RyzenGatto/Ai-HDL-MacroPad/Pictures/V1.5 MacroPad PCB.PNG

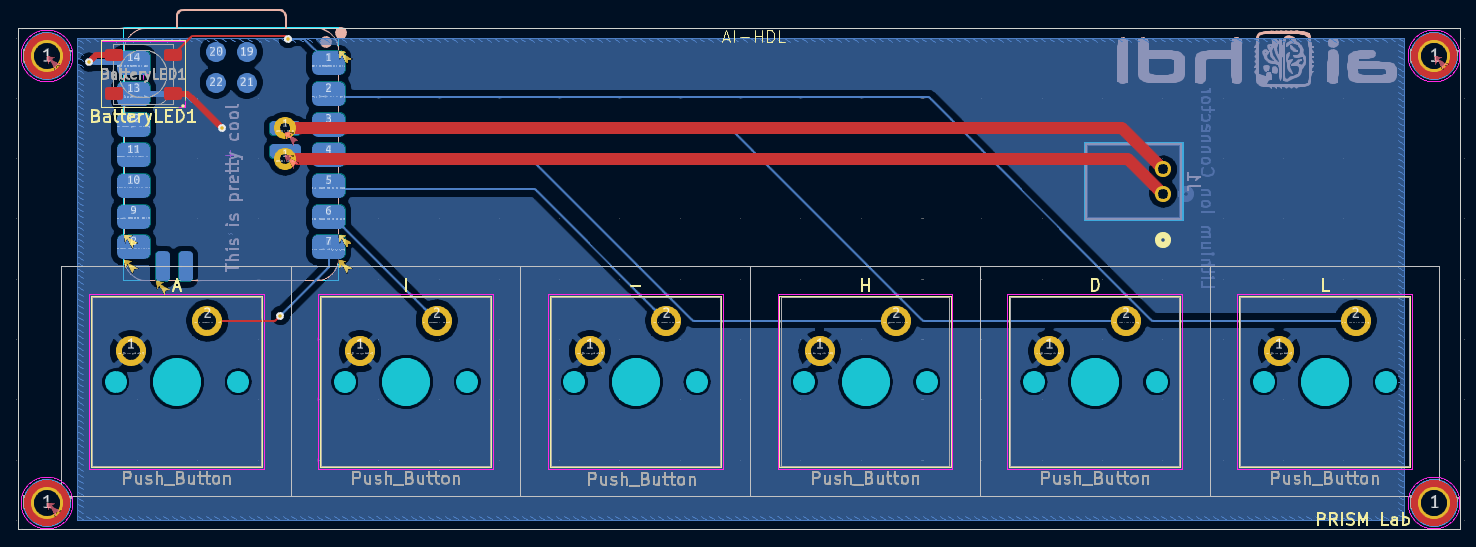
Pictures/V1.5 MacroPad PCB.PNG
